speetb/scopefocus/PCB01.PNG

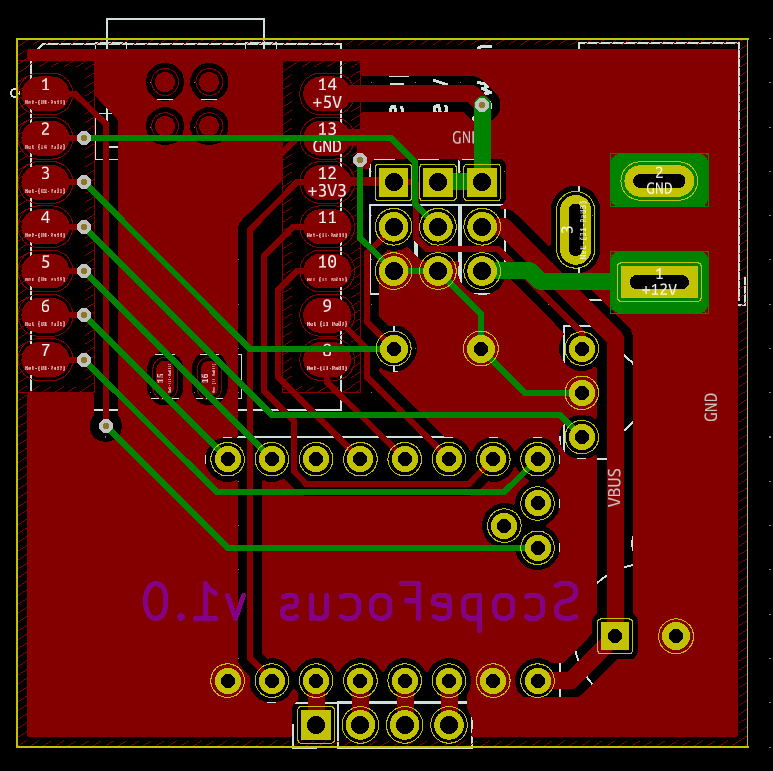
PCB01.PNG
